kellerlabs/homeracker/models/pinpusher/test/pinpusher.scad

// HomeRacker - Pin Pusher Test
//
// Test file for pin pusher module.

include <../parts/pinpusher.scad>
