kellerlabs/homeracker/models/core/test/support.scad

// HomeRacker - Support
//
// Fully customizable support beam part.

// Use the main homeracker library file
include <../main.scad>

units = 17;
x_holes = true;
support(units = units, x_holes = x_holes);
