kellerlabs/homeracker/models/inception/test/supportgrid.scad

// HomeRacker - Support Grid Test
//
// Test file for support grid module.

include <../lib/supportgrid.scad>

supportgrid(hr_width = 11, hr_height = 3, funnel_strength = 3, grid_depth = 1);
