kellerlabs/homeracker/cmd/scadfmt/tests/canary/canary.expected.scad

// scadfmt canary: every OpenSCAD construct, badly formatted on purpose.
// canary.expected.scad holds the exact formatter output; check.sh verifies both against OpenSCAD.
include <canary_missing.scad>
use <canary_missing.scad>

/* [Section] */
width = 10;         // [1:100]
depth = 20;         // aligned run
height_total = 30;  // aligned run
$fn = 32;


/* [Hidden] */
numbers = [1, 2.5, .5, 1e3, 1.5E-3, -4];
strings = ["a", "b\"c", "tab\t", "unicode ☺"];
flags = [true, false, undef];
range_a = [0:10];
range_b = [0:2:10];
range_neg = [-5:-1:-10];
arith = 1 + 2 - 3 * 4 / 5 % 6 ^ 2;
compare = [1 < 2, 1 > 2, 1 <= 2, 1 >= 2, 1 == 2, 1 != 2];
logic = !true && false || !(false);
bitwise = [5 & 3, 5 | 3, ~5, 1 << 4, 16 >> 2];
hex = [0xFF, 0x0a];
unary_after_header = [let(a = 1) -a, for (i = [1:2]) -i];
fn_negate = function (x) -x;
unary = [-width, +width, - -width];
ternary = width > 5 ? "big" : width > 2 ? "mid" : "small";
index = numbers[0] + numbers[1];
member = [1, 2, 3].x;
fn_literal = function (x) x * 2;
applied = fn_literal(3);
nested_fn = function (a, b = 2) function (c) a + b + c;
comprehension = [for (i = [0:3]) if (i % 2 == 0) i];
comprehension_else = [for (i = [0:3]) if (i > 1) i else -i];
comprehension_let = [for (i = [0:3]) let(j = i * 2) each [j, j + 1]];
c_style = [for (i = 0, j = 1; i < 3; i = i + 1, j = j * 2) j];
let_expr = let(a = 1, b = a + 1) a * b;
assert_expr = assert(width > 0, "width must be positive") width;
echo_expr = echo("width", width) width;
multi_line_list = [
  1,
  2,
  3
];
multi_line_expr = width +
  depth +
  height_total;

function square(x) = x * x;

function chained(mode) =
  mode == 1
  ? "one"
  : mode == 2
  ? "two"
  : "many";

module box(size = [1, 1, 1], center = false) {
  cube(size, center = center);
}

module wrapper() {
  children();
  children(0);
  echo($children);
}

module multi_line_signature(first = 1,
  second = 2) {
  echo(first, second);
}

translate([0, 0, width]) rotate([0, 90, 0]) box([1, 2, 3]);
translate([width, 0, 0])
  rotate([0, 0, 45])
    box();
if (width > 5) {
  box();
} else if (width > 2) {
  box([2, 2, 2]);
} else {
  box([3, 3, 3]);
}
if (width > 1)
  box();
else
  sphere(1);
if (width > 1)
  if (width > 2)
    box();
  else
    sphere(2);
else
  sphere(3);
for (i = [0:2]) {
  translate([i * 10, 0, 0]) cube(1);
}
intersection_for (i = [0:1]) {
  rotate([0, 0, i * 45]) cube(10, center = true);
}
#box();
%box();
*box();
!box();
translate([1, 0, 0]) #box();
difference() {
  cube(10);
  #translate([1, 1, 1]) cube(8);
}
wrapper() {
  sphere(1);
  cube(1);
}
let(a = 1) translate([a, 0, 0]) cube(1);
assert(true);
echo(str("done ", width));
rotate_extrude(angle = 90) square([1, 2]);
/* inline */ cube(1 /* size */);

module empty() {}

// fmt: off
aligned_by_hand = [
    1,   0,   0,
    0,   1,   0,
];
// fmt: on
last_line = 1;
