kellerlabs/homeracker/.github/actions/setup-openscad/README.md

# Setup OpenSCAD Action

Composite GitHub Action that installs OpenSCAD, system dependencies, and libraries via [scadm](../../../cmd/scadm/README.md), with caching.

> ⚠️ Requires `ubuntu` runners (uses `apt` for system dependencies).

## Why

Setting up OpenSCAD in CI requires installing system packages, downloading binaries, and managing library dependencies. This action handles all of that in a single step, with caching for fast subsequent runs.

## Usage

### Cross-repository

```yaml
steps:
  - uses: actions/checkout@v6

  - name: Setup OpenSCAD
    uses: kellerlabs/homeracker/.github/actions/setup-openscad@setup-openscad-v2
    with:
      scadm-requirements: requirements.txt
```

> Requires a `scadm.json` in the repo root. See [scadm docs](../../../cmd/scadm/README.md) for config format.

### Within homeracker

```yaml
steps:
  - uses: actions/checkout@v6

  - name: Setup OpenSCAD
    uses: ./.github/actions/setup-openscad
    with:
      scadm-source: cmd/scadm
```

## Inputs

| Input | Description | Default |
|---|---|---|
| `scadm-version` | Pinned scadm PyPI version. Takes precedence over `scadm-requirements`. | _(empty)_ |
| `scadm-requirements` | Path to a `requirements.txt` containing a pinned scadm version (e.g. `scadm==0.6.3`). Used when `scadm-version` is not set. | _(empty)_ |
| `scadm-source` | Local path for editable scadm install. Overrides both `scadm-version` and `scadm-requirements`. | _(empty)_ |

> **Priority:** `scadm-source` > `scadm-version` > `scadm-requirements`. At least one must be provided.

## What it does

1. Sets up Python 3.x
2. Installs system dependencies (`xvfb`, `libglu1-mesa`, `libfuse2`, `libegl1`, `libxcb-cursor0`)
3. Resolves scadm version from inputs (source > explicit version > requirements file)
4. Caches `bin/openscad/` keyed on runner OS, resolved scadm version, `scadm.json`, and `**/constants.py` under `scadm-source` (when set)
5. Installs [scadm](../../../cmd/scadm/README.md), pinned from PyPI, or from a local path if `scadm-source` is set
6. Runs `scadm install` to download OpenSCAD and libraries

## Versioning

This action is independently versioned via [release-please](https://github.com/googleapis/release-please). Use a pinned tag:

```yaml
uses: kellerlabs/homeracker/.github/actions/setup-openscad@setup-openscad-v2.0.0
```
