kellerlabs/homeracker/models/panel/test/renders/rackpanel.png

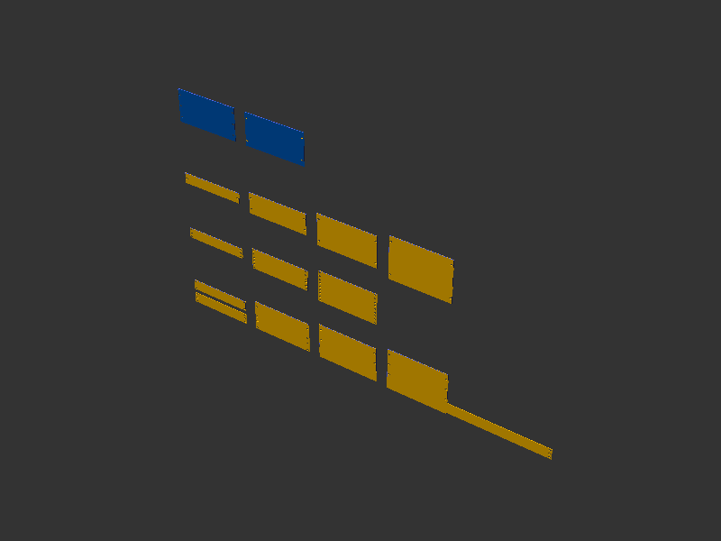
models/panel/test/renders/rackpanel.png
