kellerlabs/homeracker/.github/actions/sync-instructions/CHANGELOG.md

# Changelog

## [1.2.2](https://github.com/kellerlabs/homeracker/compare/sync-instructions-v1.2.1...sync-instructions-v1.2.2) (2026-09-27)

### 🐛 Bug Fixes

* **ci:** pass action inputs via env and enforce zizmor template-injection ([#510](https://github.com/kellerlabs/homeracker/issues/510)) ([74e77b1](https://github.com/kellerlabs/homeracker/commit/74e77b1e9474b3bb67c7fc0fdd77b05a5aec6229))

## [1.2.1](https://github.com/kellerlabs/homeracker/compare/sync-instructions-v1.2.0...sync-instructions-v1.2.1) (2026-09-14)

### ♻️ Code Refactoring

* **instructions:** make AGENTS.md canonical and align docs with house-style ([#484](https://github.com/kellerlabs/homeracker/issues/484)) ([ef337d5](https://github.com/kellerlabs/homeracker/commit/ef337d57ba903edb2602e5dc6b36c18c2fe36a8d))

## [1.2.0](https://github.com/kellerlabs/homeracker/compare/sync-instructions-v1.1.0...sync-instructions-v1.2.0) (2026-04-18)

### ✨ Features

* migrate images to assets repo, add MakerWorld extract/publish tooling ([#337](https://github.com/kellerlabs/homeracker/issues/337)) ([5d9da76](https://github.com/kellerlabs/homeracker/commit/5d9da76d5f84bbecef7da5db18597922c3c17d41))

## [1.1.0](https://github.com/kellerlabs/homeracker/compare/sync-instructions-v1.0.0...sync-instructions-v1.1.0) (2026-04-12)

### ✨ Features

* **sync-instructions:** discover instruction files dynamically ([#336](https://github.com/kellerlabs/homeracker/issues/336)) ([7321560](https://github.com/kellerlabs/homeracker/commit/7321560dc0b7eb19f90a20bf1e87f4e2ed16003d))

## 1.0.0 (2026-03-20)

### 🔧 Miscellaneous

* **sync-instructions:** address PR review feedback ([00f4b4c](https://github.com/kellerlabs/homeracker/commit/00f4b4c1c450cdccdcfe07f07e46165a1efdc0a6))
